Neumi/fastLOGIC/hardware/version002/fastLOGIC/3d_files/TERMINAL_BLOCKS_141r/DG141R-2-2.54.step

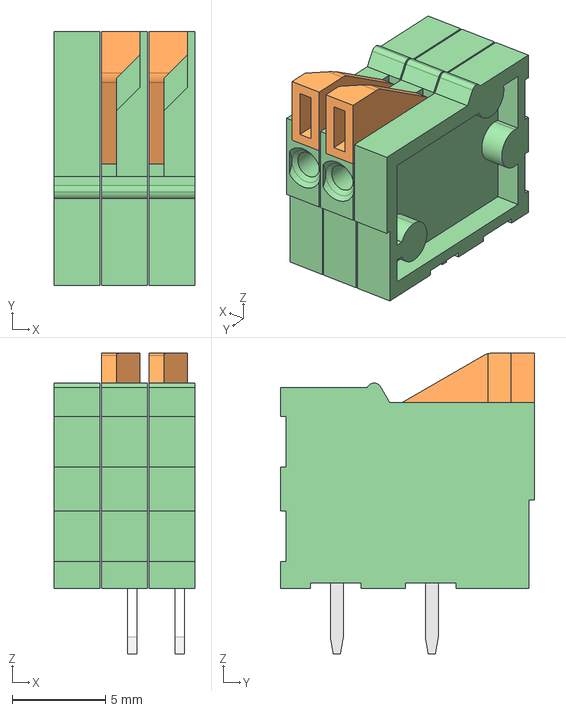
[picture p26: CAD file, 2024-12-31]
hardware/version002/fastLOGIC/3d_files/TERMINAL_BLOCKS_141r/DG141R-2-2.54.step
7.52 x 13.6 x 16.1 mm
