Neumi/fastLOGIC/hardware/version002/fastLOGIC/3d_files/TMC2209.STEP

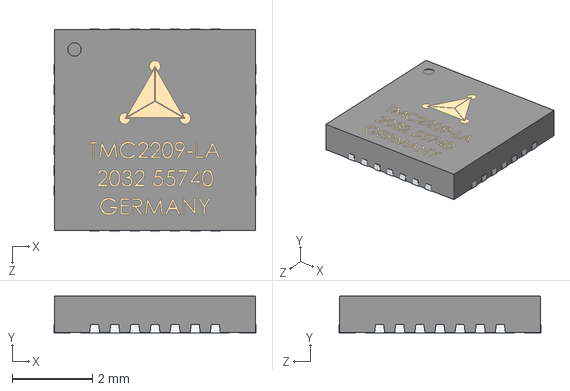
[picture p27: CAD file, 2024-12-31]
hardware/version002/fastLOGIC/3d_files/TMC2209.STEP
5.02 x 0.911 x 5.02 mm
