Neumi/fastLOGIC/hardware/version002/fastLOGIC/3d_files/Mini-B USB Vertical.stp

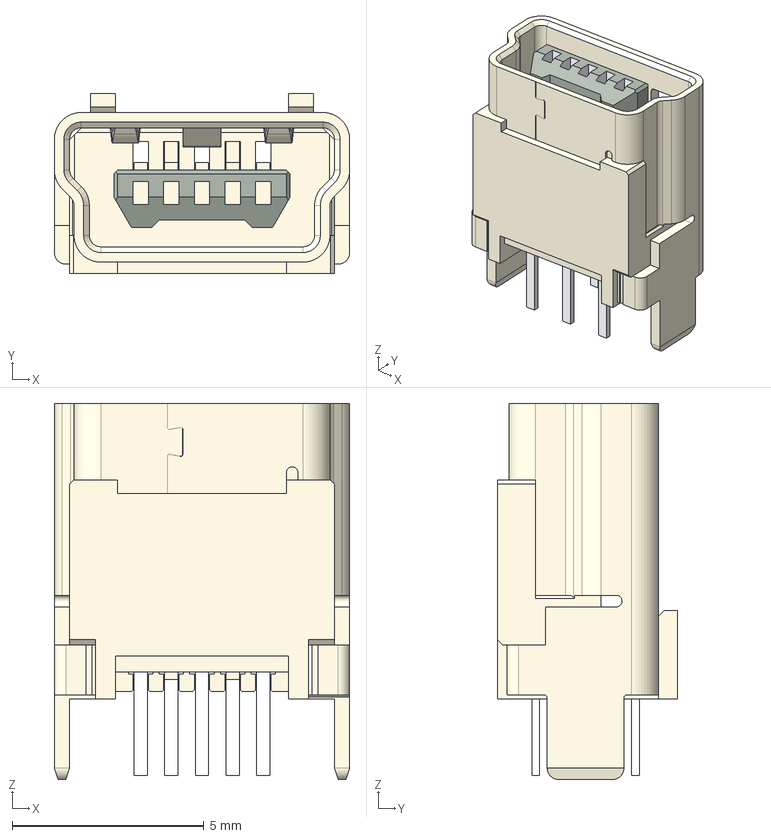
[picture p28: CAD file, 2023-12-06]
hardware/version002/fastLOGIC/3d_files/Mini-B USB Vertical.stp
7.70 x 4.70 x 9.80 mm
