Neumi/fastLOGIC/hardware/version002/fastLOGIC/3d_files/TERMINAL_BLOCKS_141r/DG141R-3-2.54.step

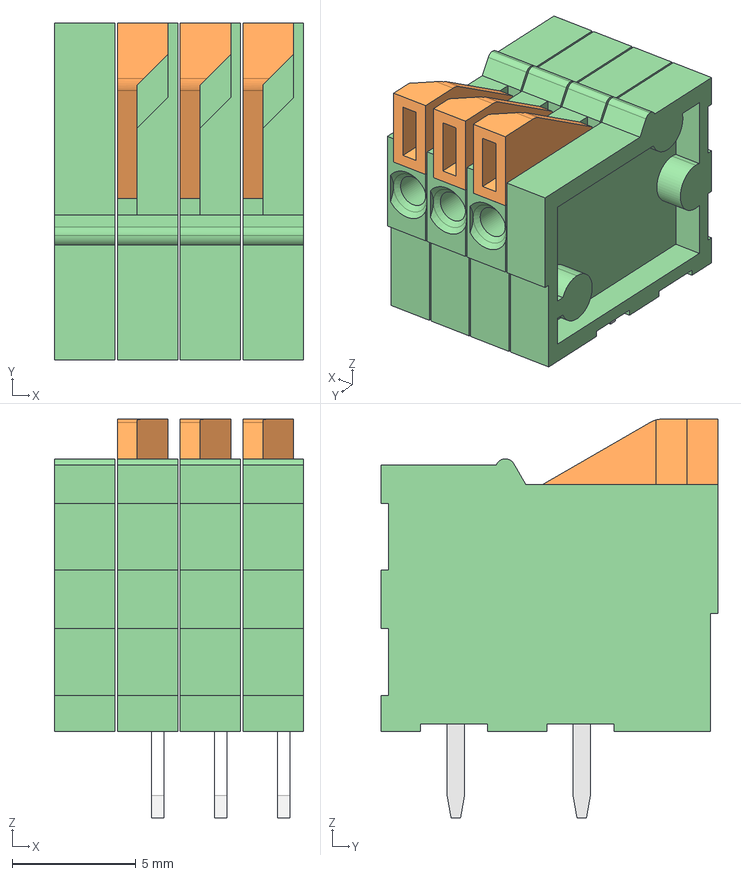
[picture p30: CAD file, 2024-12-31]
hardware/version002/fastLOGIC/3d_files/TERMINAL_BLOCKS_141r/DG141R-3-2.54.step
10.1 x 13.6 x 16.1 mm
