Neumi/fastLOGIC/hardware/version002/fastLOGIC/3d_files/TERMINAL_BLOCKS_141r/DG141R-12-2.54.step

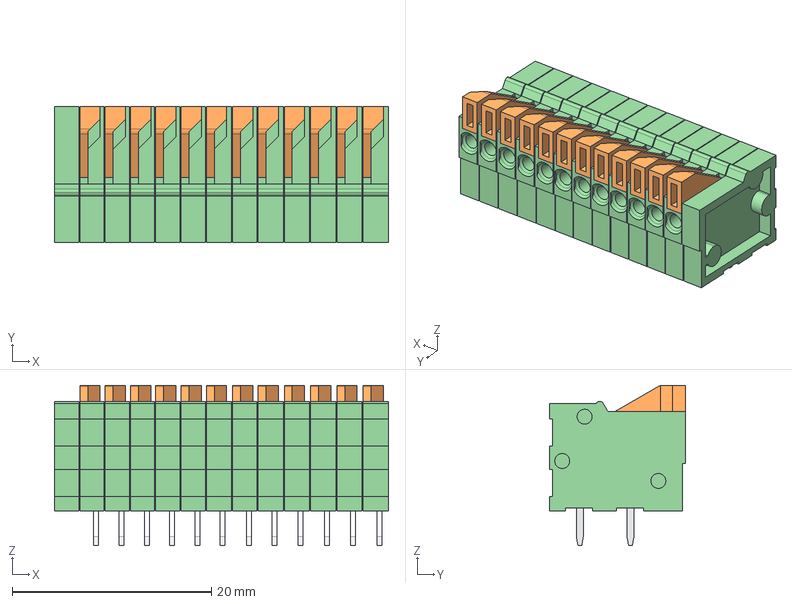
[picture p31: CAD file, 2024-12-31]
hardware/version002/fastLOGIC/3d_files/TERMINAL_BLOCKS_141r/DG141R-12-2.54.step
33.5 x 13.6 x 16.1 mm
Тело_29 - Копия_4:4 x 6
Тело_29 - Копия_4:3 x 6
Тело_29 - Копия_4:2 x 6
Тело_29 - Копия_4:1 x 6
Тело_11 - Внешняя модель_11:2 x 2
Тело_12 - Внешняя модель_12:2 x 2
Тело_20 - Внешняя модель_20:2 x 2
Тело_14 - Внешняя модель_14:2 x 2
