Neumi/fastLOGIC/hardware/version002/fastLOGIC/3d_files/TS-1187A.step

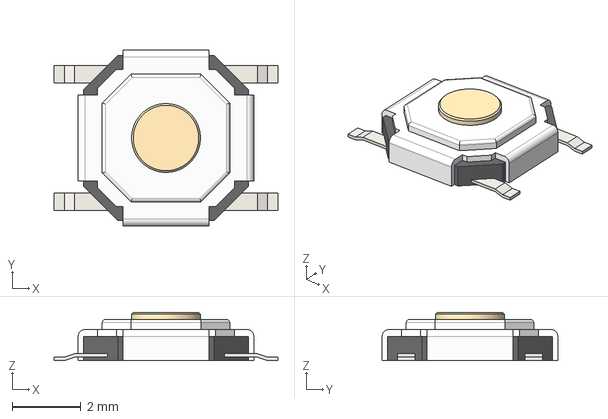
[picture p32: CAD file, 2023-12-06]
hardware/version002/fastLOGIC/3d_files/TS-1187A.step
6.50 x 5.10 x 1.40 mm
