Neumi/fastLOGIC/hardware/version002/fastLOGIC/3d_files/PCB Terminal Block 3 DEG381-3.5.step

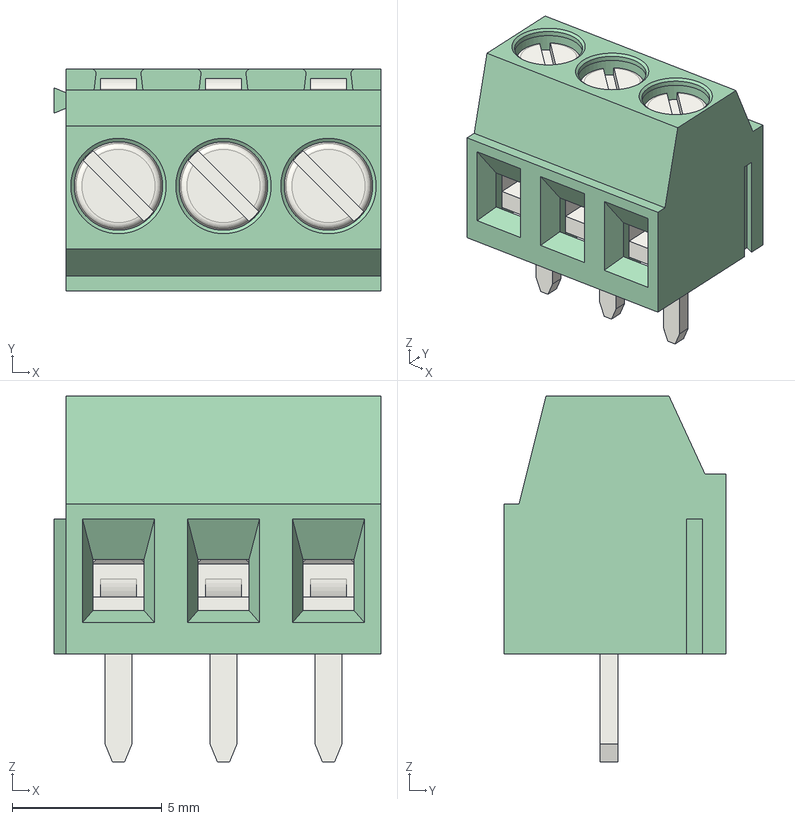
[picture p33: CAD file, 2023-12-06]
hardware/version002/fastLOGIC/3d_files/PCB Terminal Block 3 DEG381-3.5.step
10.9 x 7.40 x 12.2 mm
Plastic Housing002
Pin 003
Clamp Block002
M1.6x3-Screw002
