Neumi/fastLOGIC/hardware/version002/fastLOGIC/3d_files/PCB Terminal Block 2 DEG381-3.5.step

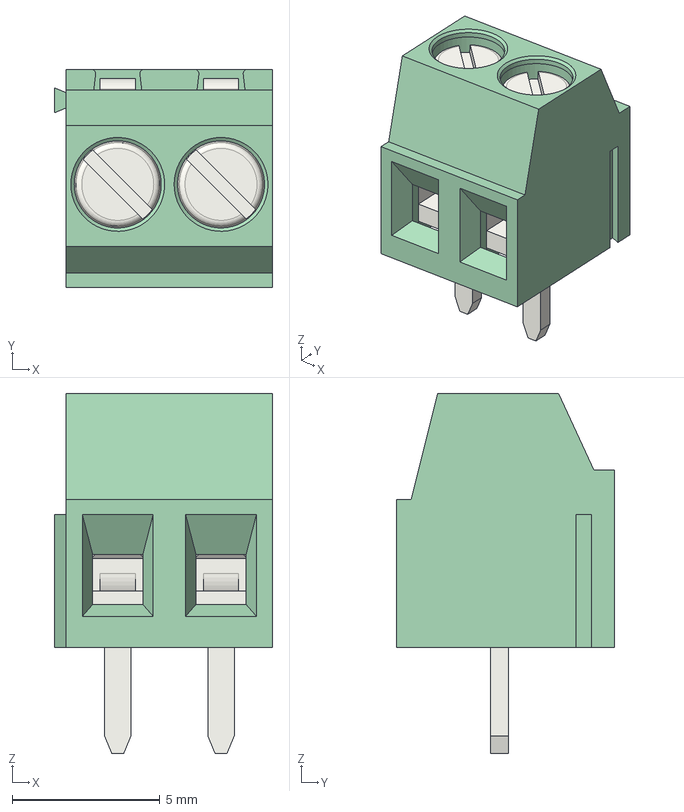
[picture p34: CAD file, 2023-12-06]
hardware/version002/fastLOGIC/3d_files/PCB Terminal Block 2 DEG381-3.5.step
7.40 x 7.40 x 12.2 mm
Plastic Housing001
Pin 002
Clamp Block001
M1.6x3-Screw001
