Neumi/fastLOGIC/hardware/version002/fastLOGIC/3d_files/XGZP6847A.STEP

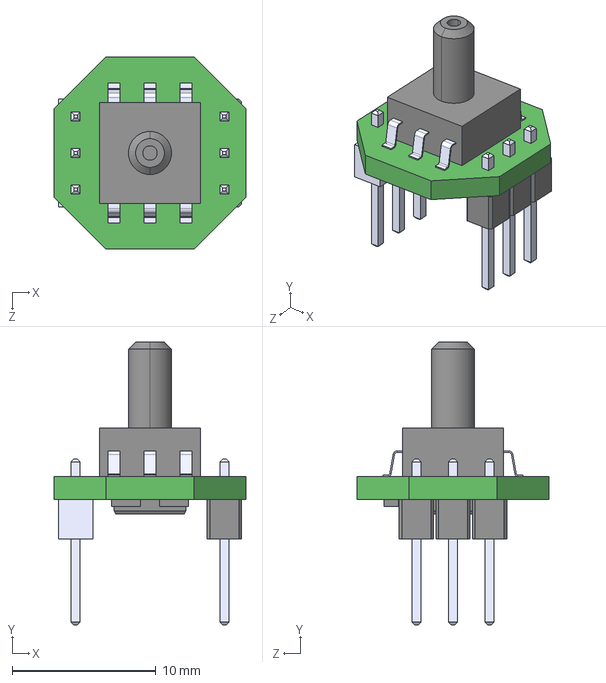
[picture p35: CAD file, 2023-12-06]
hardware/version002/fastLOGIC/3d_files/XGZP6847A.STEP
13.4 x 19.7 x 13.3 mm
